telzo2000/cool436/img/img00011.jpg

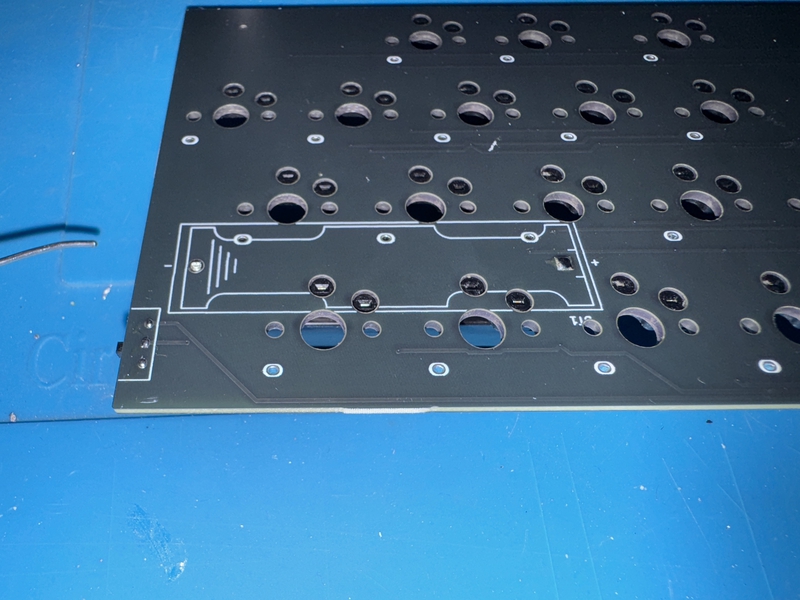
img/img00011.jpg
